RepRapLtd/6DInput/RepRapLtd/Pictures/force-sensor-cad-600x600.jpg

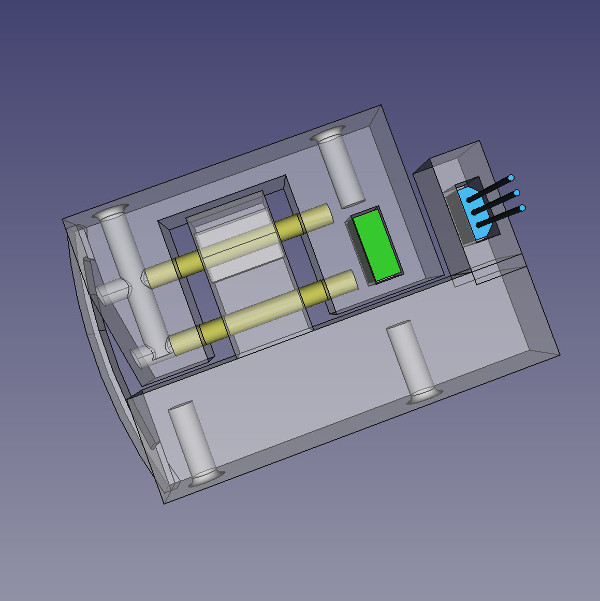
RepRapLtd/Pictures/force-sensor-cad-600x600.jpg
