RepRapLtd/6DInput/RepRapLtd/Pictures/force-sensor-cad.jpg

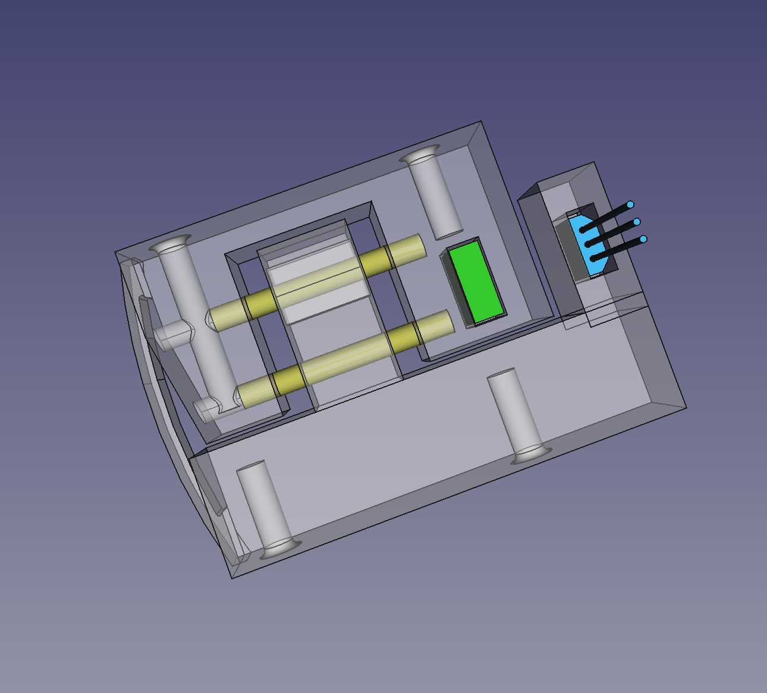
RepRapLtd/Pictures/force-sensor-cad.jpg
