RepRapLtd/6DInput/RepRapLtd/Pictures/force-sensor.jpg

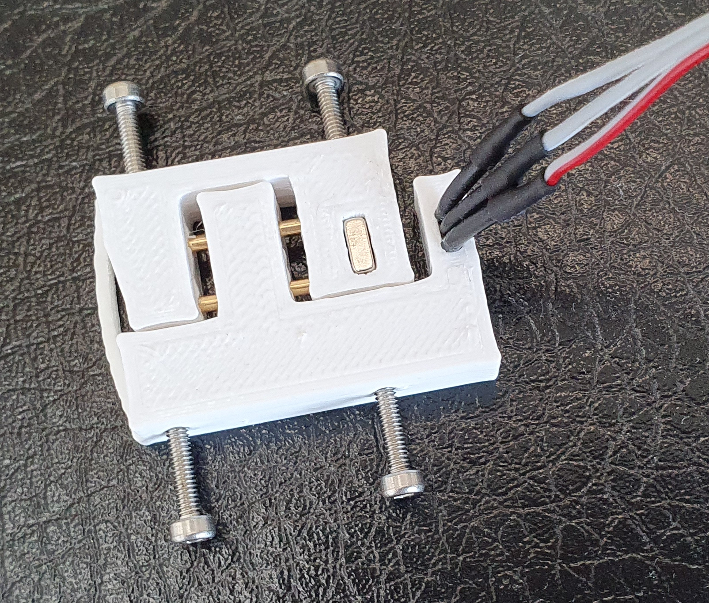
RepRapLtd/Pictures/force-sensor.jpg
