RepRapLtd/6DInput/RepRapLtd/Pictures/nintendo.png

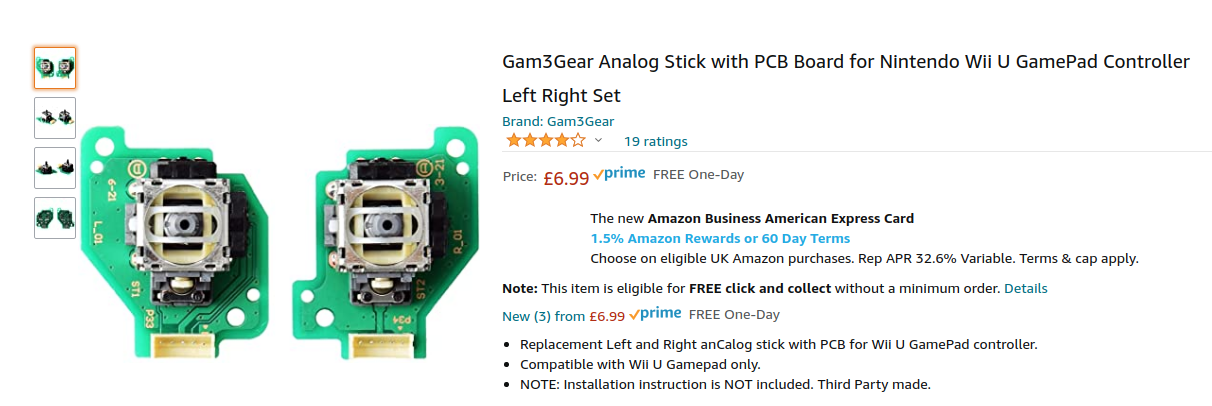
RepRapLtd/Pictures/nintendo.png
