RepRapLtd/6DInput/RepRapLtd/Pictures/v1-cad.jpg

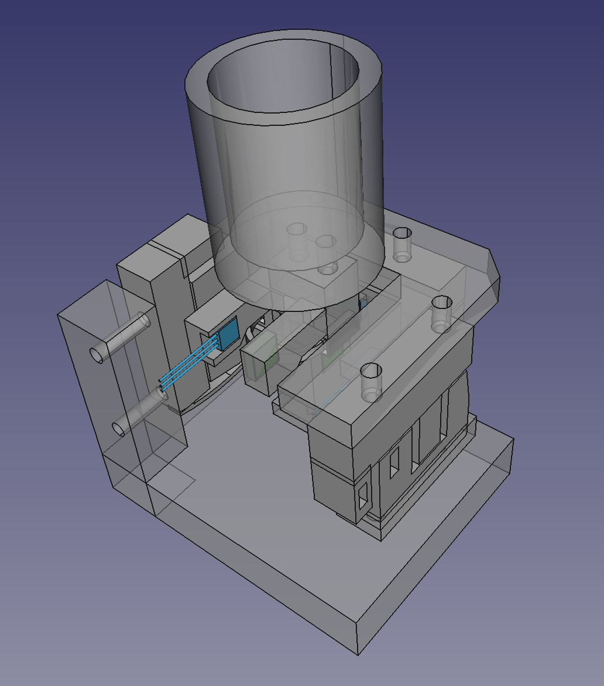
RepRapLtd/Pictures/v1-cad.jpg
