RepRapLtd/6DInput/RepRapLtd/Pictures/v1.jpg

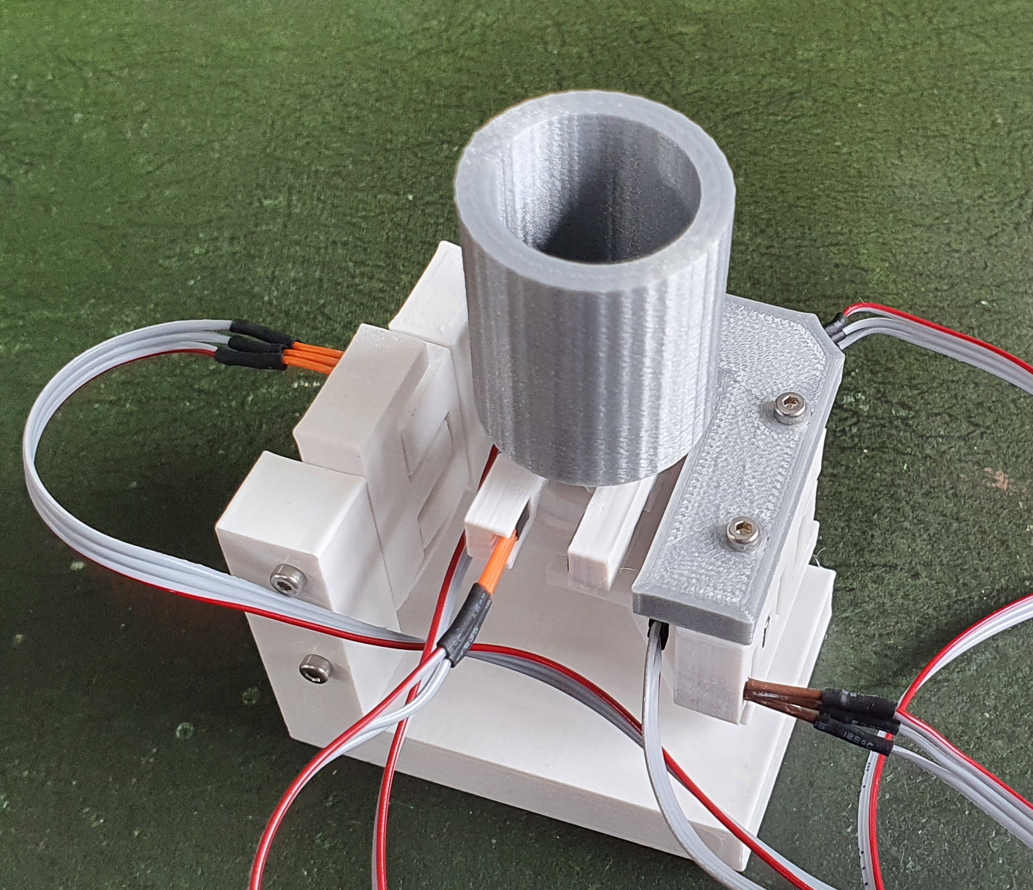
RepRapLtd/Pictures/v1.jpg
