RepRapLtd/6DInput/RepRapLtd/Pictures/XYZ-joystick-CAD-600.png

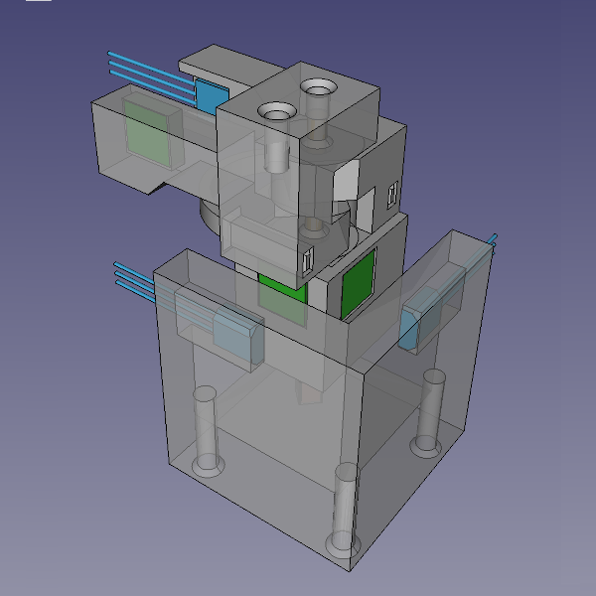
RepRapLtd/Pictures/XYZ-joystick-CAD-600.png
