RepRapLtd/6DInput/RepRapLtd/Mechanics/STLs/6DOF-disc-wright-base.stl

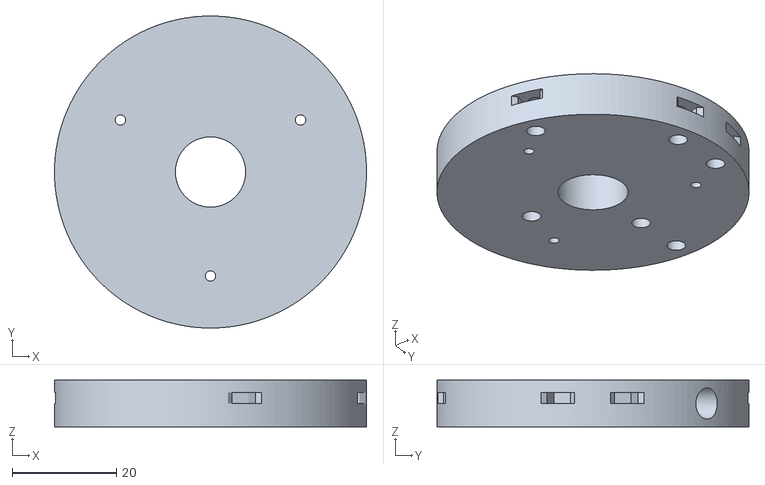
[picture p35: CAD file, 2021-08-13]
RepRapLtd/Mechanics/STLs/6DOF-disc-wright-base.stl
60.0 x 60.0 x 9.00
