RepRapLtd/6DInput/Mechanics/Assembly Experiments/3D Printable Joystick Assembly - Magnetic Encoders/Parts/AS5247UAdapterBoard.FCStd

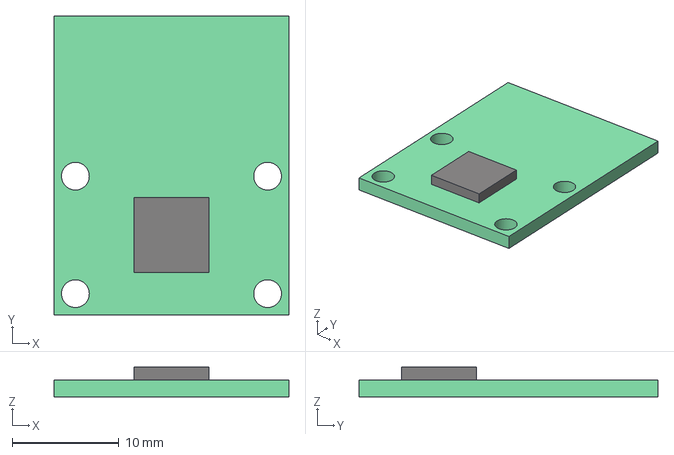
[picture p36: CAD file, 2021-05-03]
Mechanics/Assembly Experiments/3D Printable Joystick Assembly - Magnetic Encoders/Parts/AS5247UAdapterBoard.FCStd
22.0 x 28.0 x 2.80 mm
PCB
IC
