RepRapLtd/6DInput/RepRapLtd/Mechanics/OS3Dmouse-V1.FCStd

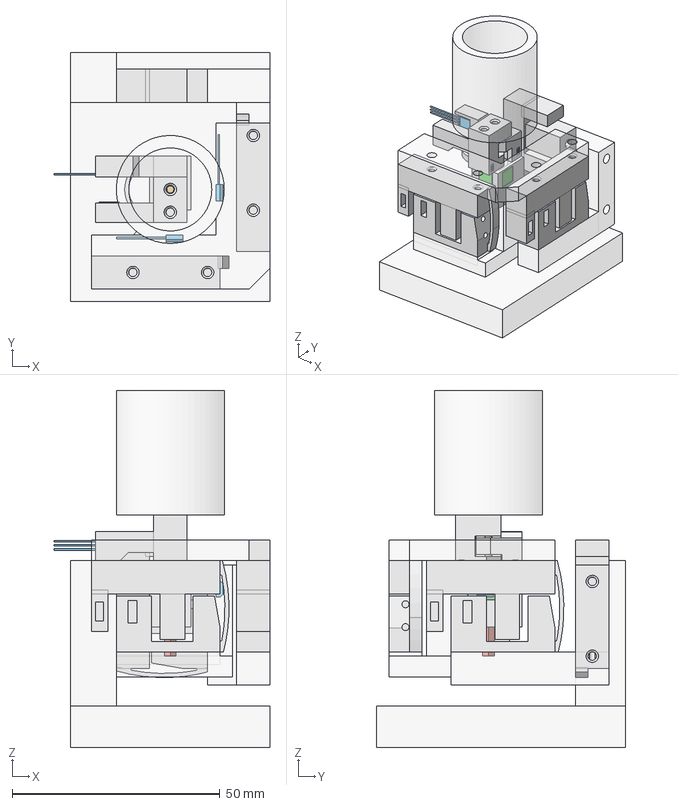
[picture p37: CAD file, 2021-06-14]
RepRapLtd/Mechanics/OS3Dmouse-V1.FCStd
52.0 x 60.0 x 86.0 mm
top-spring
magnet
sensor-OH49E-b
sensor-OH49E-a
magnet-5x5x2-b
magnet-5x5x2-a
bottom-spring
lever
magnet-5x5x2-c
sensor-OH49E-c
rod004
force-sensor
force-sensor001
force-sensor002
handle
XY-link
rot-x-link
YZ-link
base
