RepRapLtd/6DInput/RepRapLtd/Mechanics/STLs/6DoF-disc-base.stl

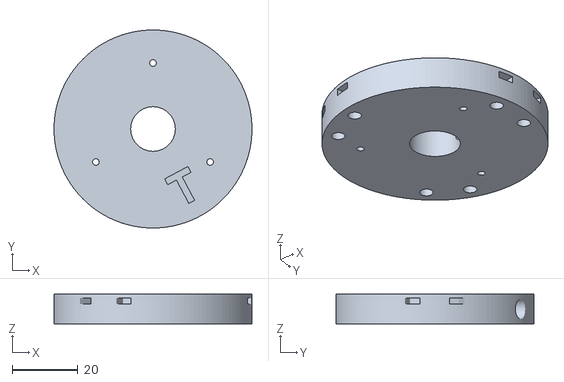
[picture p38: CAD file, 2021-08-02]
RepRapLtd/Mechanics/STLs/6DoF-disc-base.stl
60.0 x 60.0 x 9.00
