RepRapLtd/6DInput/Mechanics/Assembly Experiments/3D Printable Joystick Assembly - Magnetic Encoders/Parts/GimbalMount.FCStd

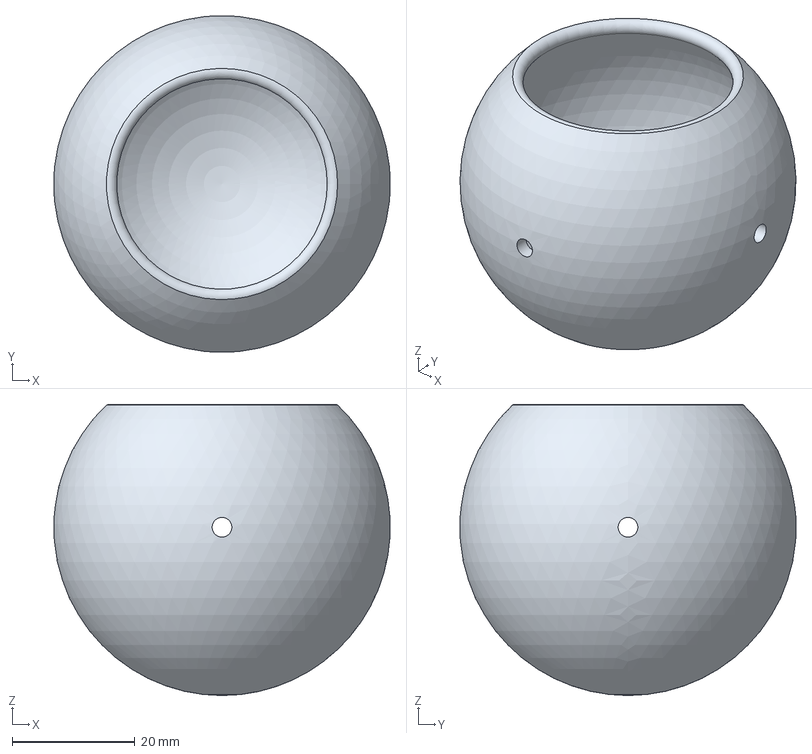
[picture p39: CAD file, 2021-05-03]
Mechanics/Assembly Experiments/3D Printable Joystick Assembly - Magnetic Encoders/Parts/GimbalMount.FCStd
54.7 x 54.7 x 47.4 mm
