RepRapLtd/6DInput/RepRapLtd/Mechanics/6DOF-cones.FCStd

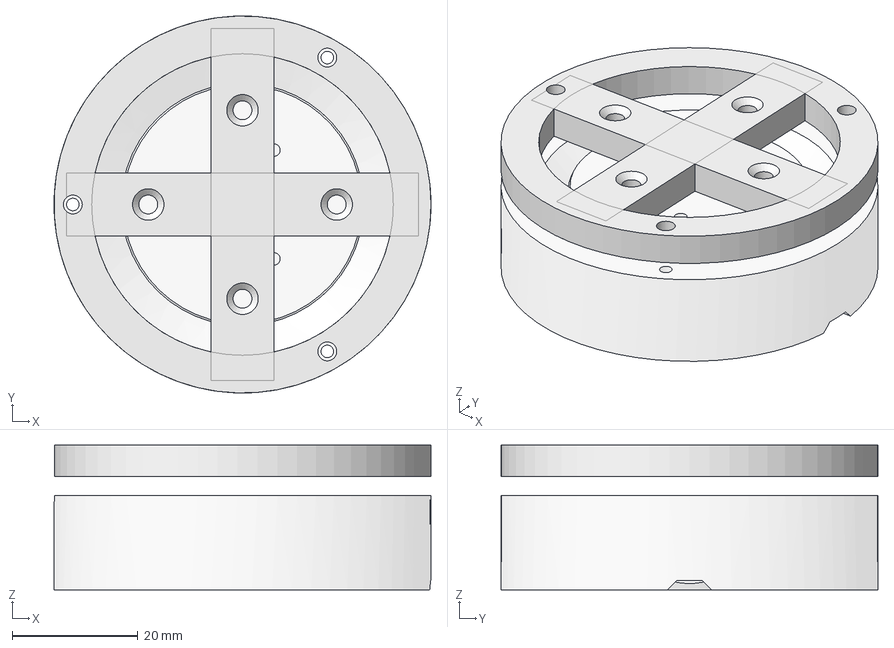
[picture p40: CAD file, 2021-06-11]
RepRapLtd/Mechanics/6DOF-cones.FCStd
60.0 x 60.0 x 23.0 mm
hall-f
magnet-f
calibration
