RepRapLtd/6DInput/RepRapLtd/Mechanics/STLs/6DoF-disc-handle.stl

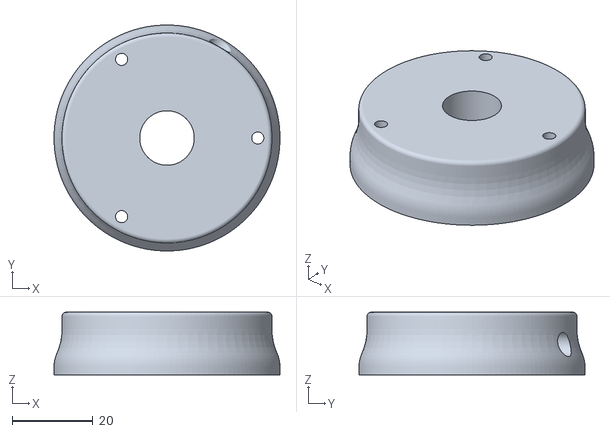
[picture p41: CAD file, 2021-08-02]
RepRapLtd/Mechanics/STLs/6DoF-disc-handle.stl
56.0 x 56.0 x 15.5
