RepRapLtd/6DInput/Mechanics/Assembly Experiments/3D Printable Joystick Assembly - Magnetic Encoders/Parts/DiametricMagnet8x2.5mm.FCStd

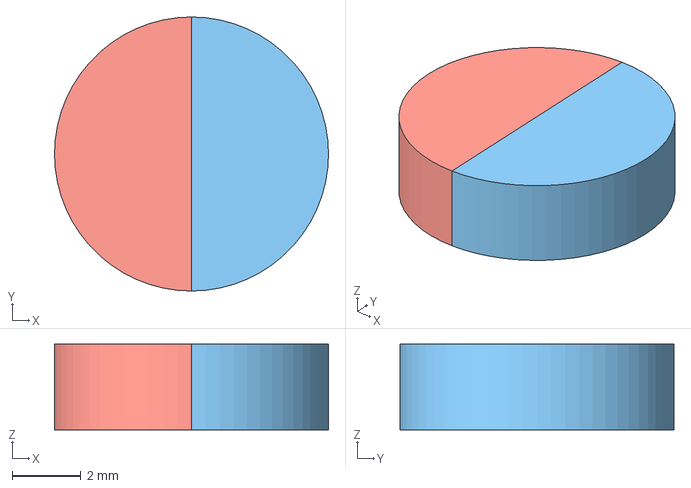
[picture p42: CAD file, 2021-05-03]
Mechanics/Assembly Experiments/3D Printable Joystick Assembly - Magnetic Encoders/Parts/DiametricMagnet8x2.5mm.FCStd
8.00 x 8.00 x 2.50 mm
North
South
