RepRapLtd/6DInput/RepRapLtd/Mechanics/STLs/6DoF-disc-spring-clamp.stl

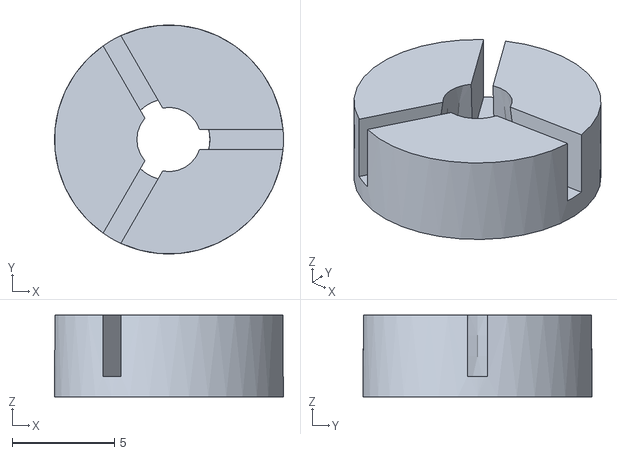
[picture p43: CAD file, 2021-07-16]
RepRapLtd/Mechanics/STLs/6DoF-disc-spring-clamp.stl
11.2 x 11.2 x 4.00
