RepRapLtd/6DInput/RepRapLtd/Mechanics/XYZ-joystick-V1.FCStd

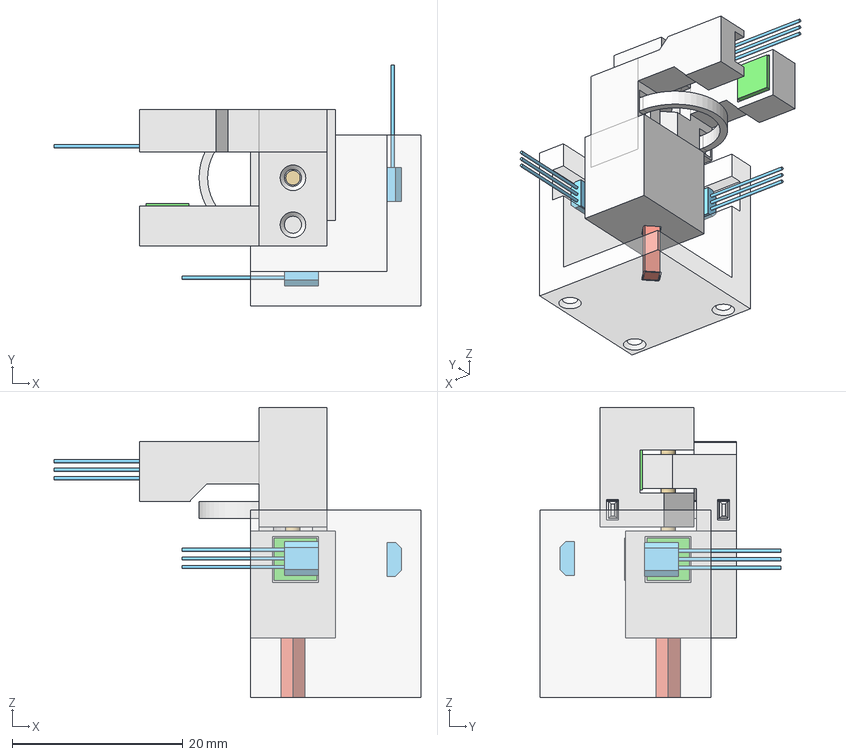
[picture p44: CAD file, 2021-06-11]
RepRapLtd/Mechanics/XYZ-joystick-V1.FCStd
43.0 x 28.2 x 34.0 mm
top-spring
magnet
sensor-OH49E-b
sensor-OH49E-a
magnet-5x5x2-b
magnet-5x5x2-a
bottom-spring
lever
magnet-5x5x2-c
sensor-OH49E-c
rod004
