RepRapLtd/6DInput/Mechanics/Assembly Experiments/3D Printable Joystick Assembly - Magnetic Encoders/Parts/Dial.FCStd

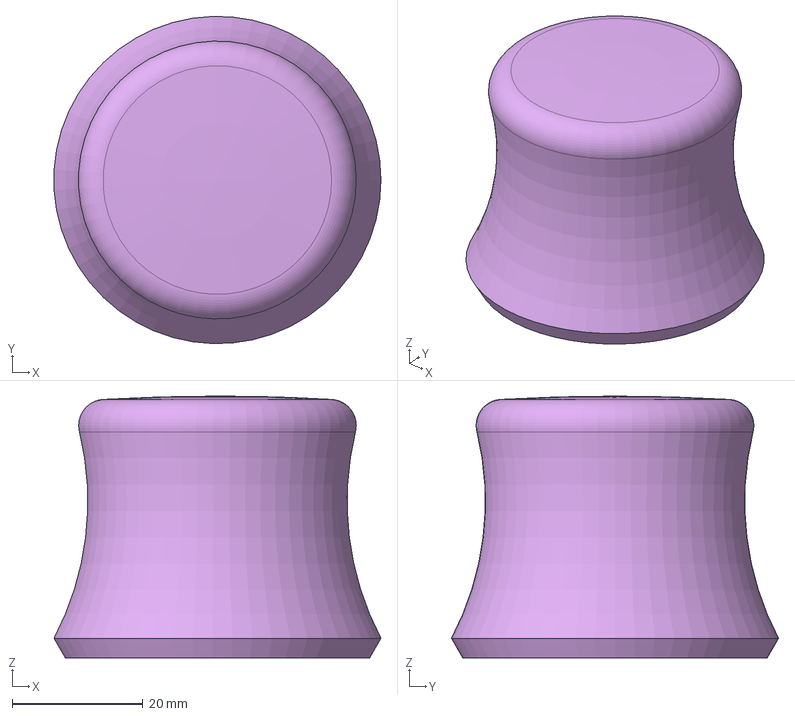
[picture p45: CAD file, 2021-05-03]
Mechanics/Assembly Experiments/3D Printable Joystick Assembly - Magnetic Encoders/Parts/Dial.FCStd
50.0 x 50.0 x 40.0 mm
