RepRapLtd/6DInput/RepRapLtd/Mechanics/STLs/OS3Dmouse-XY-link.stl

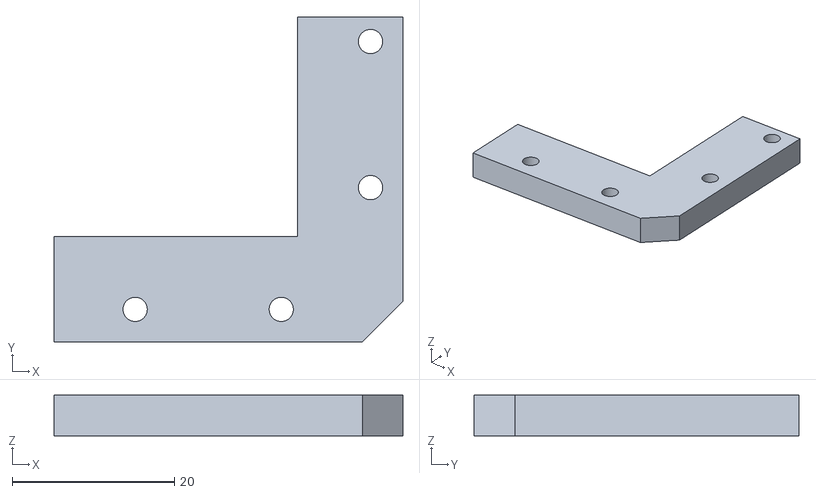
[picture p46: CAD file, 2021-06-14]
RepRapLtd/Mechanics/STLs/OS3Dmouse-XY-link.stl
43.0 x 40.0 x 5.00
