RepRapLtd/6DInput/RepRapLtd/Mechanics/torque-sensor-V3.FCStd

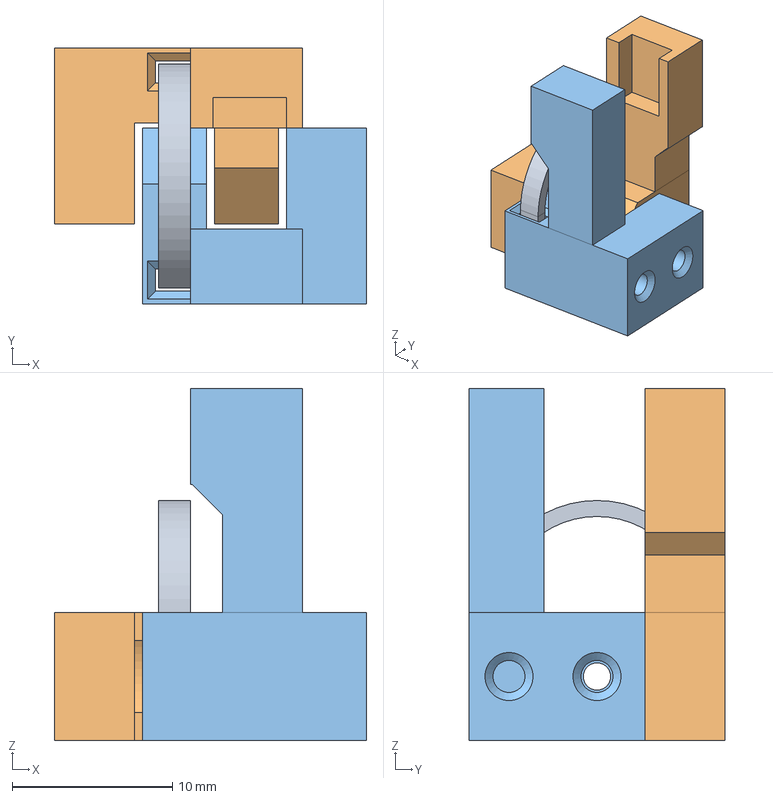
[picture p47: CAD file, 2021-06-10]
RepRapLtd/Mechanics/torque-sensor-V3.FCStd
19.5 x 16.0 x 22.0 mm
spring
hall
magnet
