RepRapLtd/6DInput/RepRapLtd/Mechanics/2D-joystick-V1.FCStd

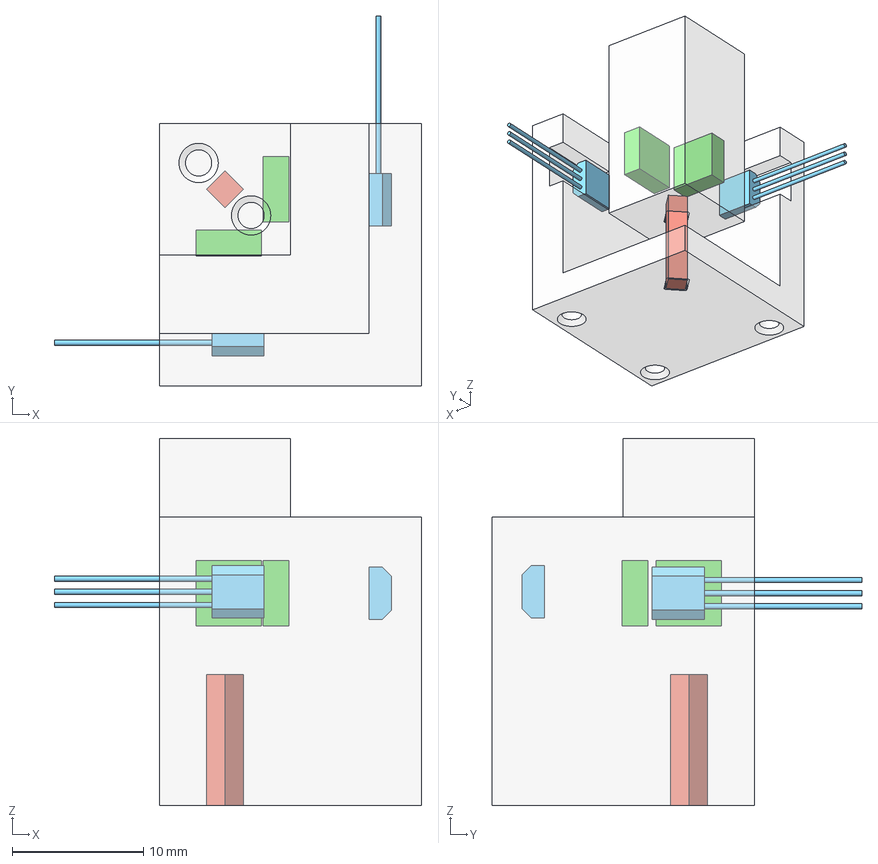
[picture p48: CAD file, 2021-06-08]
RepRapLtd/Mechanics/2D-joystick-V1.FCStd
28.0 x 28.2 x 28.0 mm
spring-0
lever
magnet-5x5x2-a
sensor-OH49E-a
magnet-5x5x2-b
sensor-OH49E-b
