RepRapLtd/6DInput/RepRapLtd/Mechanics/STLs/OS3Dmouse-YZ-link.stl

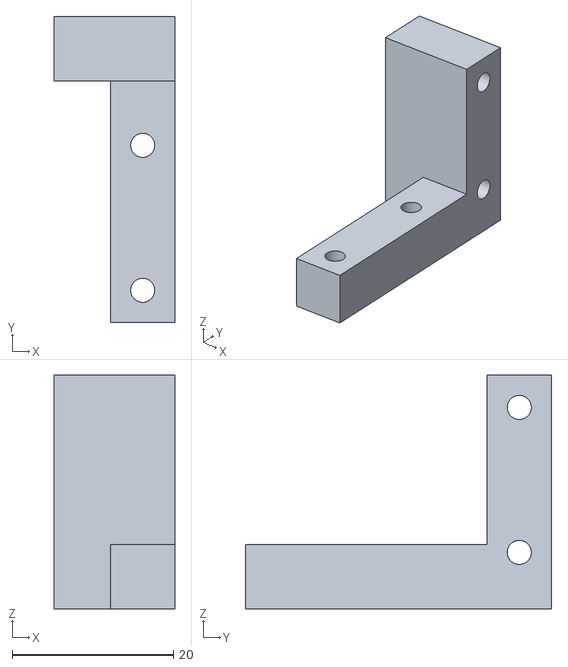
[picture p49: CAD file, 2021-06-14]
RepRapLtd/Mechanics/STLs/OS3Dmouse-YZ-link.stl
15.0 x 38.0 x 29.0
