RepRapLtd/6DInput/RepRapLtd/Mechanics/force-sensor-V1.FCStd

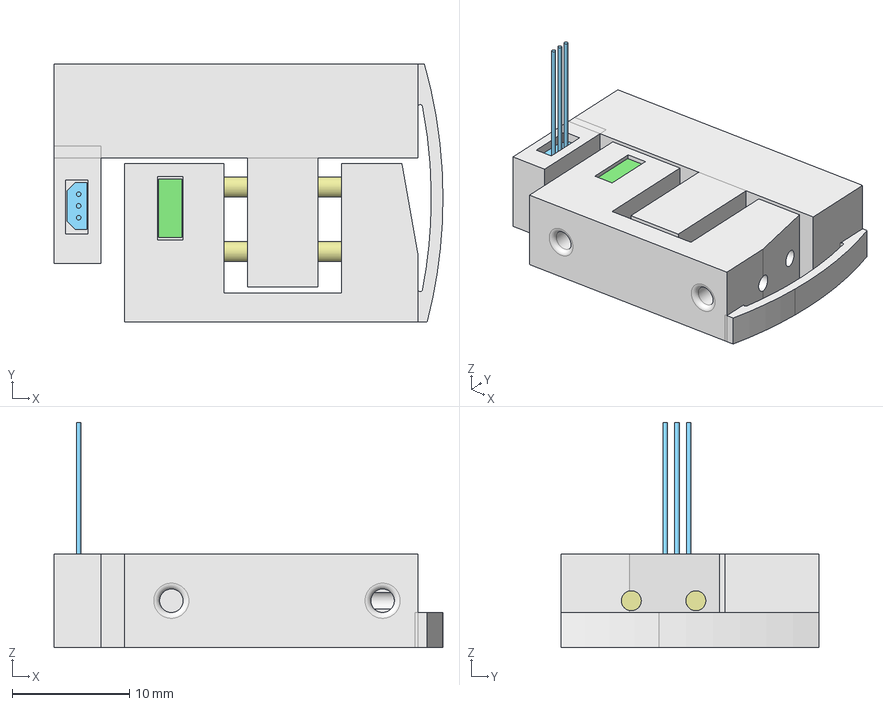
[picture p50: CAD file, 2021-06-05]
RepRapLtd/Mechanics/force-sensor-V1.FCStd
33.1 x 22.0 x 19.2 mm
force-sensor
magnet-5x5x2
sensor-OH49E
brass-rod-1
brass-rod-2
