RepRapLtd/6DInput/RepRapLtd/Mechanics/STLs/OS3Dmouse-rotX-link.stl

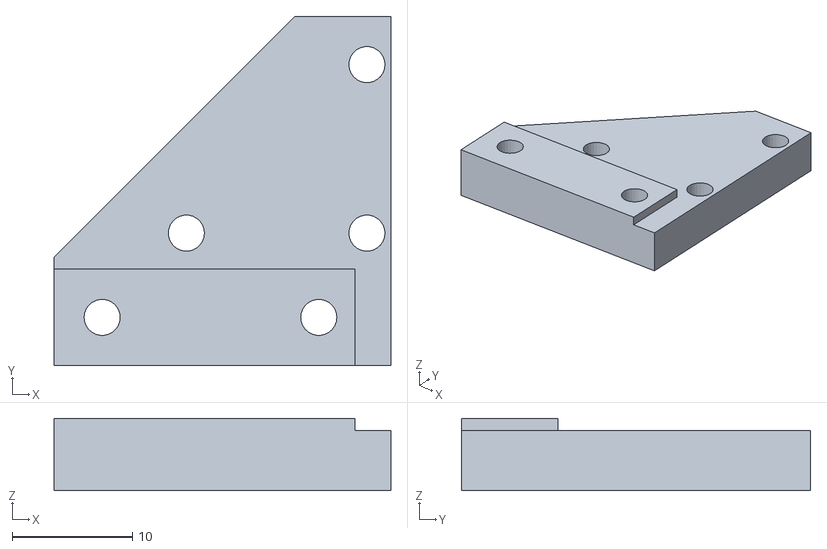
[picture p51: CAD file, 2021-06-14]
RepRapLtd/Mechanics/STLs/OS3Dmouse-rotX-link.stl
28.0 x 29.0 x 6.00
