RepRapLtd/6DInput/RepRapLtd/Mechanics/STLs/OS3Dmouse-base.stl

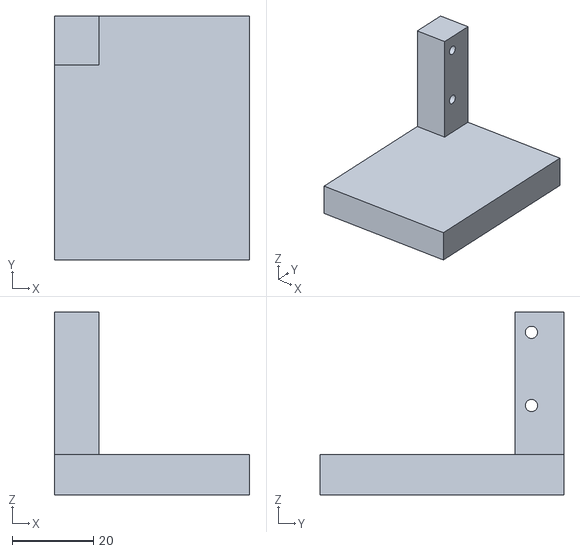
[picture p52: CAD file, 2021-06-14]
RepRapLtd/Mechanics/STLs/OS3Dmouse-base.stl
48.0 x 60.0 x 45.0
