RepRapLtd/6DInput/RepRapLtd/Mechanics/calibration-jig.FCStd

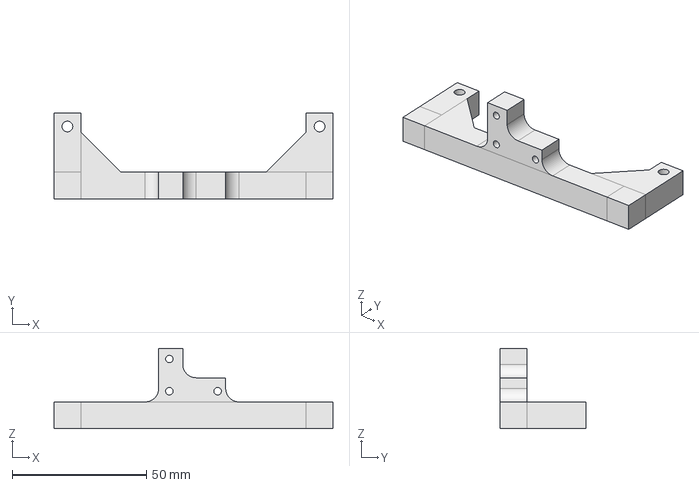
[picture p53: CAD file, 2021-05-28]
RepRapLtd/Mechanics/calibration-jig.FCStd
104.0 x 32.0 x 30.0 mm
