RepRapLtd/6DInput/RepRapLtd/Mechanics/STLs/OS3Dmouse-handle.stl

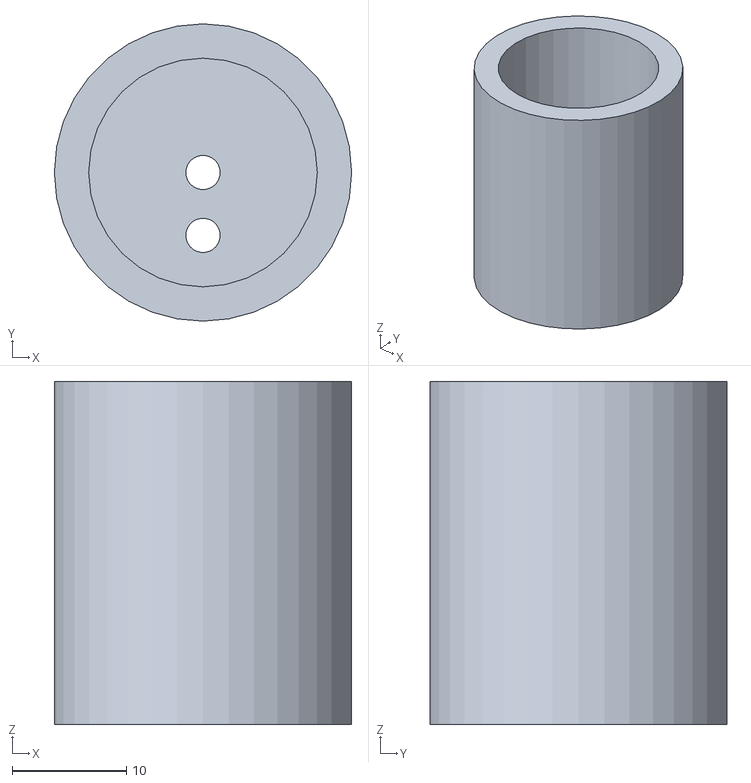
[picture p54: CAD file, 2021-06-14]
RepRapLtd/Mechanics/STLs/OS3Dmouse-handle.stl
26.0 x 26.0 x 30.0
