RepRapLtd/6DInput/RepRapLtd/Mechanics/octahedron-design.FCStd

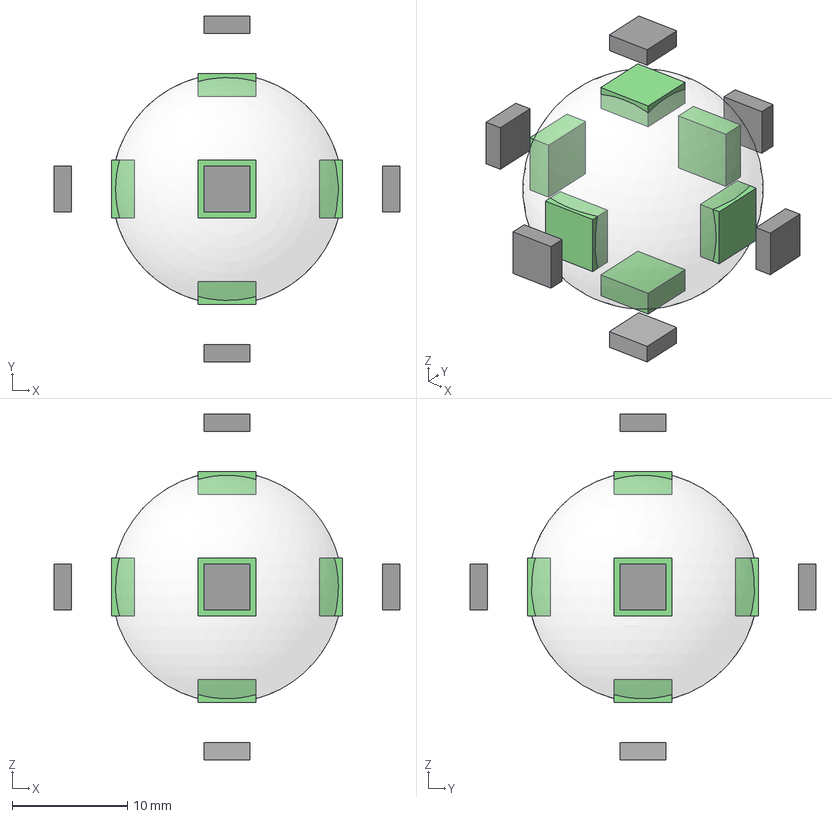
[picture p55: CAD file, 2021-05-21]
RepRapLtd/Mechanics/octahedron-design.FCStd
30.0 x 30.0 x 30.0 mm
