RepRapLtd/6DInput/RepRapLtd/Mechanics/STLs/6D-cones-magnet.stl

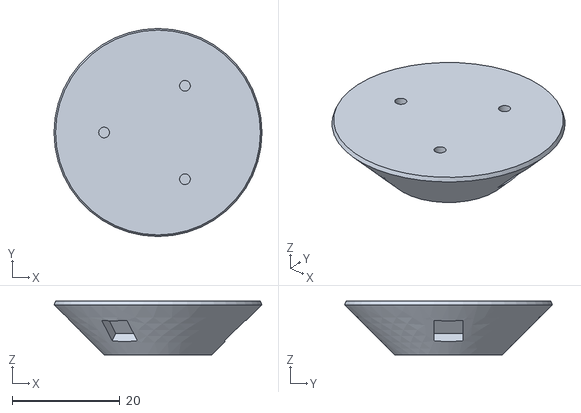
[picture p56: CAD file, 2021-06-11]
RepRapLtd/Mechanics/STLs/6D-cones-magnet.stl
38.6 x 38.6 x 10.0
