RepRapLtd/6DInput/RepRapLtd/Mechanics/force-displacement-sensor-V2.FCStd

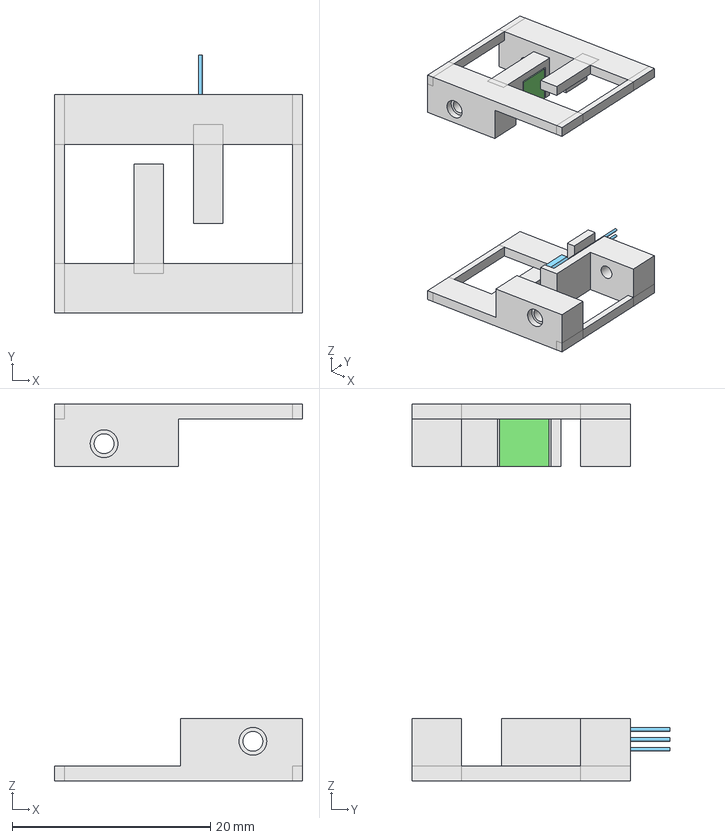
[picture p57: CAD file, 2021-05-21]
RepRapLtd/Mechanics/force-displacement-sensor-V2.FCStd
25.0 x 26.0 x 38.0 mm
hall
magnet
mag
sensor
