RepRapLtd/6DInput/RepRapLtd/Mechanics/STLs/6D-cones-calibration.stl

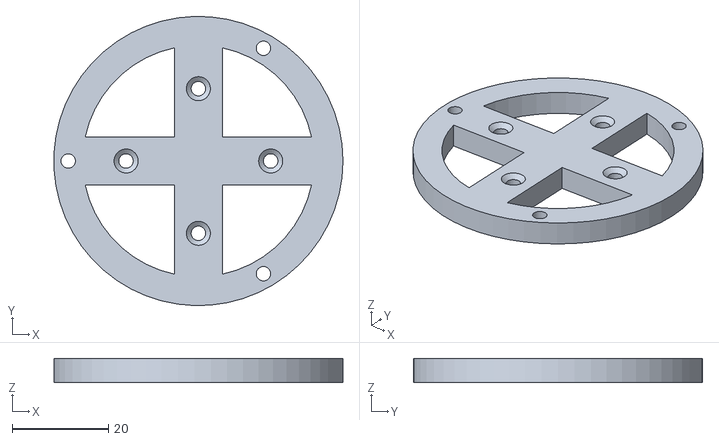
[picture p58: CAD file, 2021-06-11]
RepRapLtd/Mechanics/STLs/6D-cones-calibration.stl
60.0 x 60.0 x 5.00
