RepRapLtd/6DInput/RepRapLtd/Mechanics/STLs/6D-cones-hall.stl

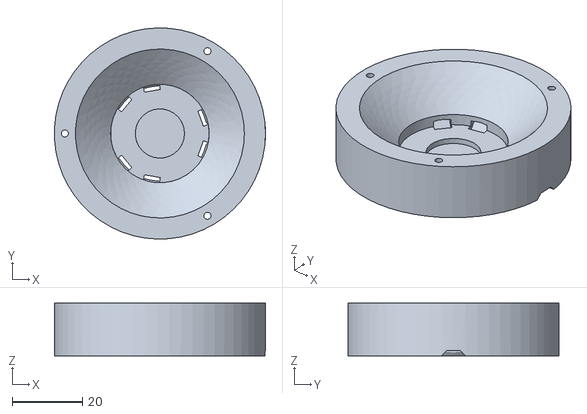
[picture p59: CAD file, 2021-06-11]
RepRapLtd/Mechanics/STLs/6D-cones-hall.stl
60.0 x 60.0 x 15.0
