RepRapLtd/6DInput/RepRapLtd/Mechanics/Hall-ring-experiment-holder.FCStd

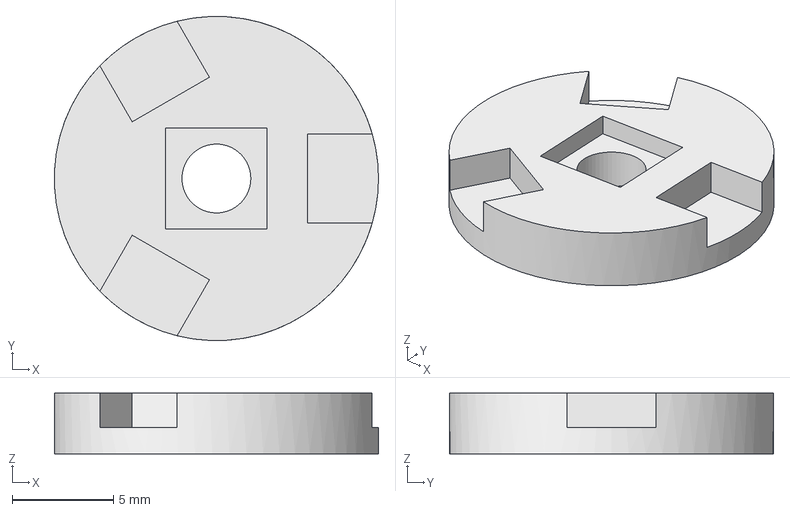
[picture p60: CAD file, 2021-05-11]
RepRapLtd/Mechanics/Hall-ring-experiment-holder.FCStd
16.0 x 16.0 x 3.00 mm
