RepRapLtd/6DInput/RepRapLtd/Mechanics/STLs/torque-hall.stl

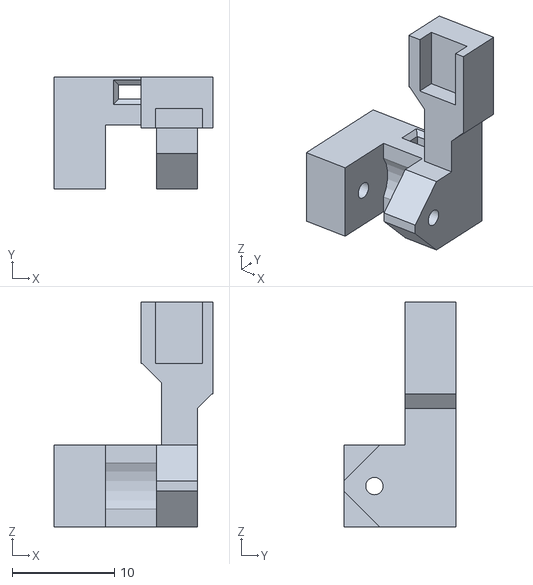
[picture p61: CAD file, 2021-06-10]
RepRapLtd/Mechanics/STLs/torque-hall.stl
15.5 x 11.0 x 22.0
