RepRapLtd/6DInput/RepRapLtd/Mechanics/STLs/XYZ-joystick-twist-spring.stl

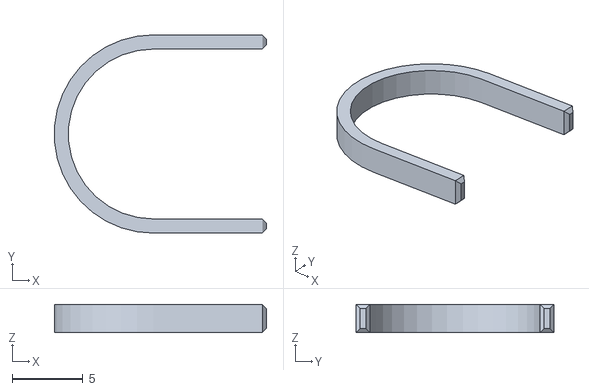
[picture p62: CAD file, 2021-06-10]
RepRapLtd/Mechanics/STLs/XYZ-joystick-twist-spring.stl
15.0 x 14.0 x 2.00
