RepRapLtd/6DInput/RepRapLtd/Mechanics/STLs/torque-magnet.stl

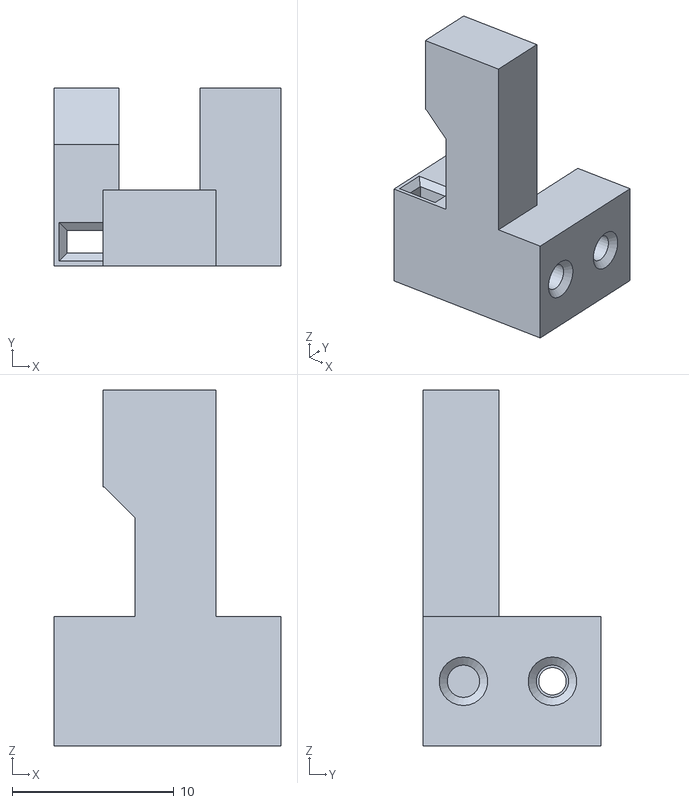
[picture p63: CAD file, 2021-06-10]
RepRapLtd/Mechanics/STLs/torque-magnet.stl
14.0 x 11.0 x 22.0
