RepRapLtd/6DInput/RepRapLtd/Mechanics/STLs/XYZ-joystick-lever.stl

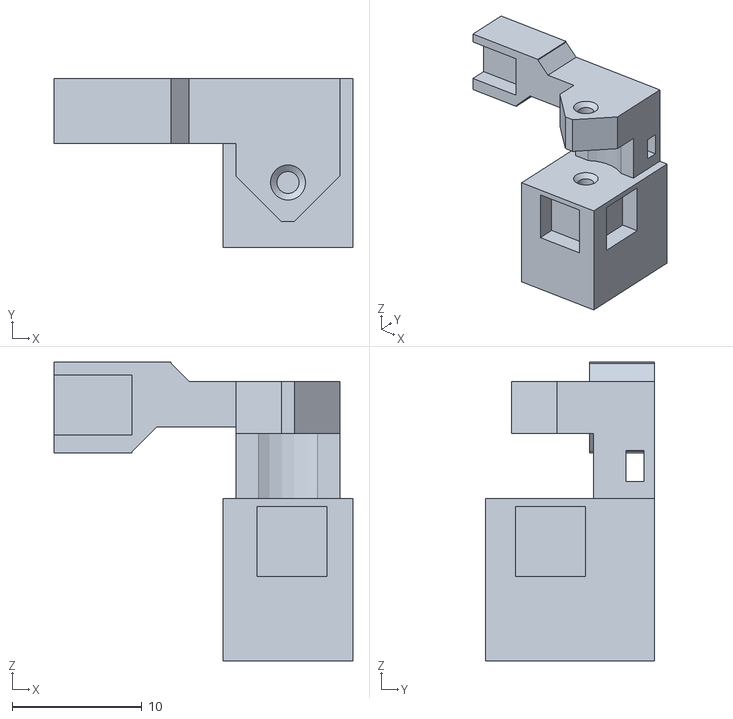
[picture p64: CAD file, 2021-06-10]
RepRapLtd/Mechanics/STLs/XYZ-joystick-lever.stl
23.0 x 13.0 x 23.0
