RepRapLtd/6DInput/RepRapLtd/Mechanics/STLs/joystick-lever.stl

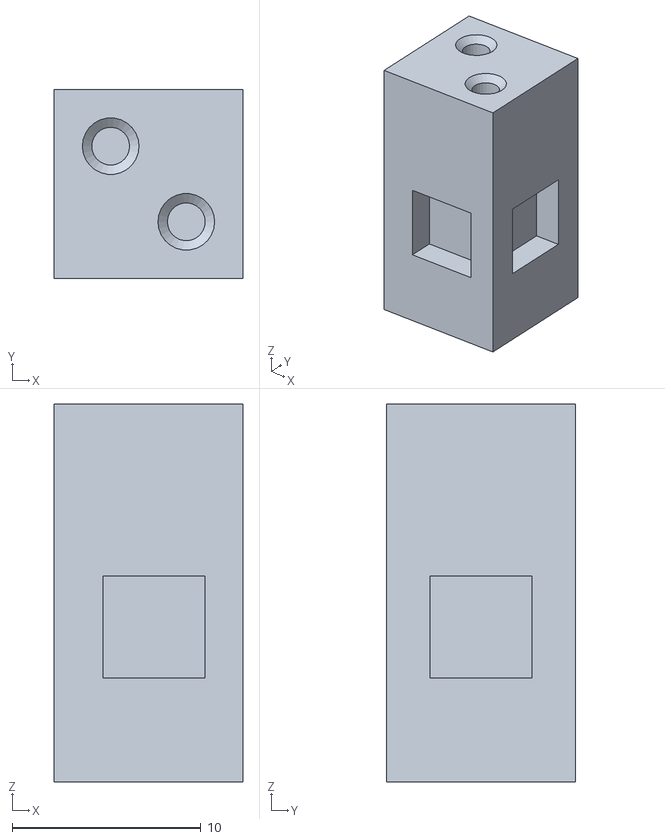
[picture p65: CAD file, 2021-06-08]
RepRapLtd/Mechanics/STLs/joystick-lever.stl
10.0 x 10.0 x 20.0
