RepRapLtd/6DInput/RepRapLtd/Mechanics/STLs/joystick-body.stl

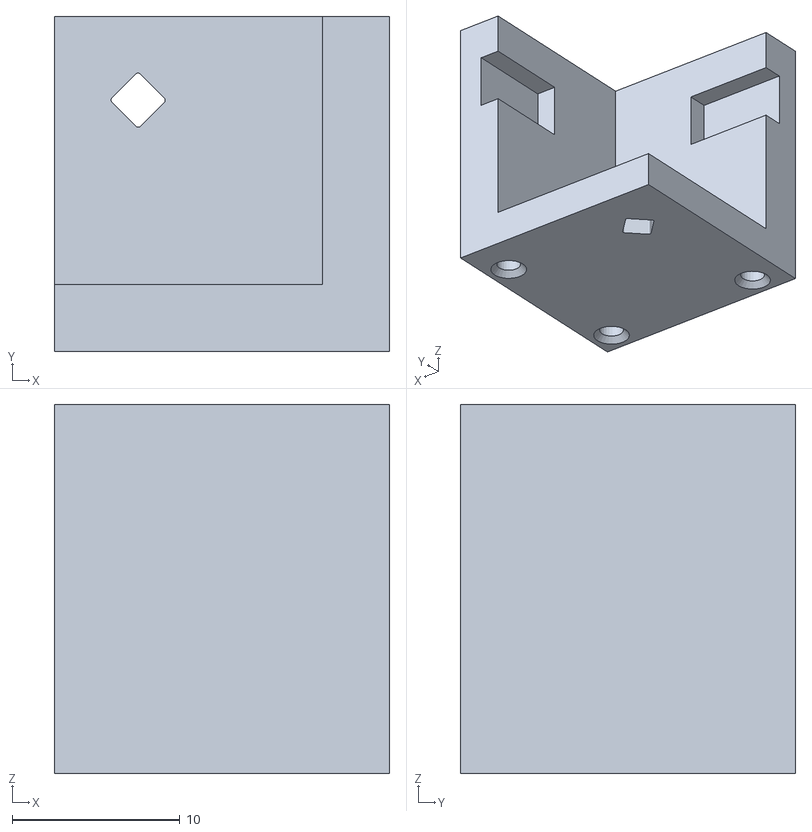
[picture p66: CAD file, 2021-06-08]
RepRapLtd/Mechanics/STLs/joystick-body.stl
20.0 x 20.0 x 22.0
