RepRapLtd/6DInput/RepRapLtd/Mechanics/STLs/joystick-spring.stl

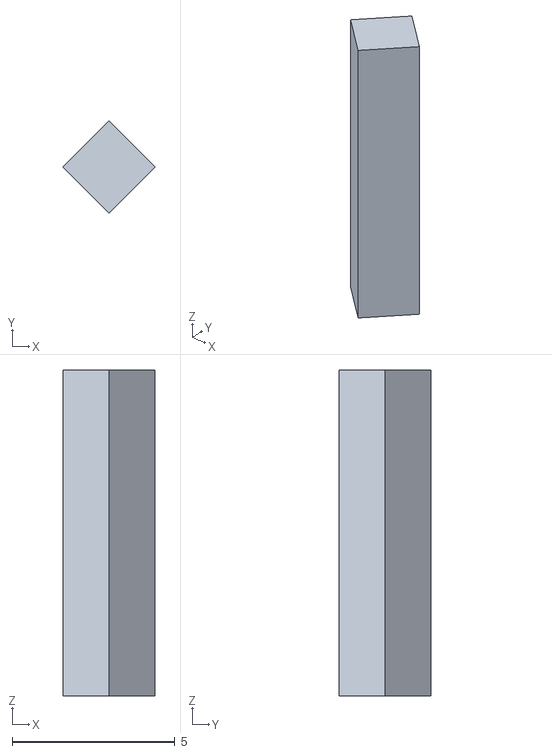
[picture p67: CAD file, 2021-06-08]
RepRapLtd/Mechanics/STLs/joystick-spring.stl
2.83 x 2.83 x 10.0
