RepRapLtd/6DInput/RepRapLtd/Mechanics/STLs/force-sensor.stl

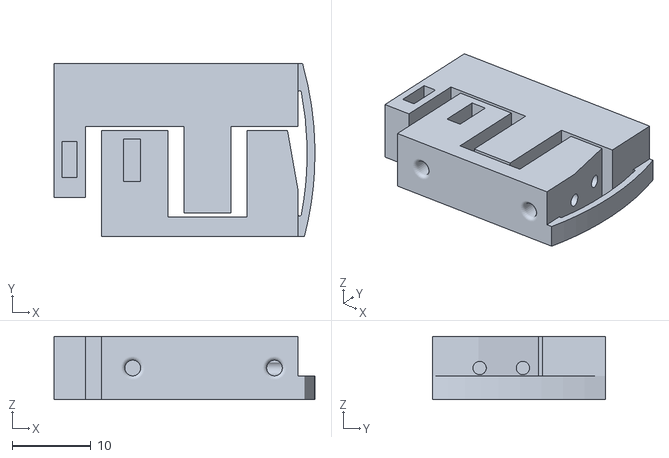
[picture p68: CAD file, 2021-05-28]
RepRapLtd/Mechanics/STLs/force-sensor.stl
33.1 x 22.0 x 8.00
