RepRapLtd/6DInput/Experiments/Geometry Tester/Example results/Magnet Distances.png

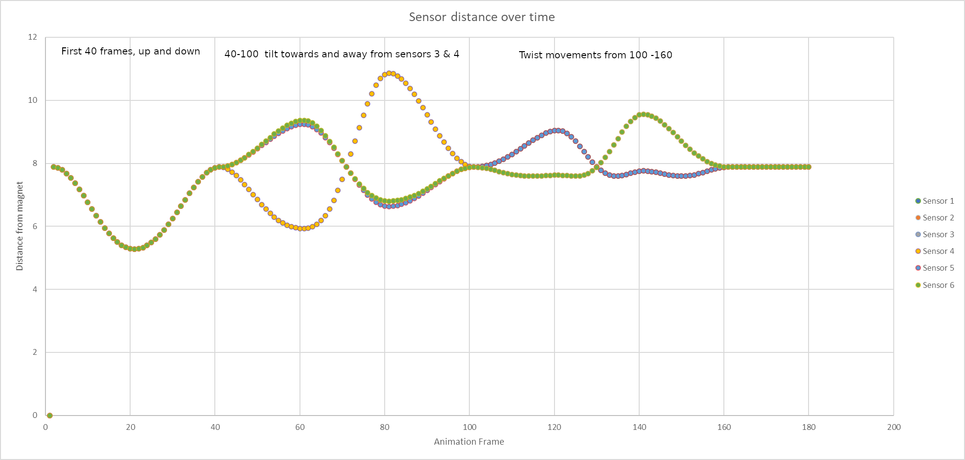
Experiments/Geometry Tester/Example results/Magnet Distances.png
