RepRapLtd/6DInput/RepRapLtd/Experiments/TorqueSensor/hinge-insert.jpg

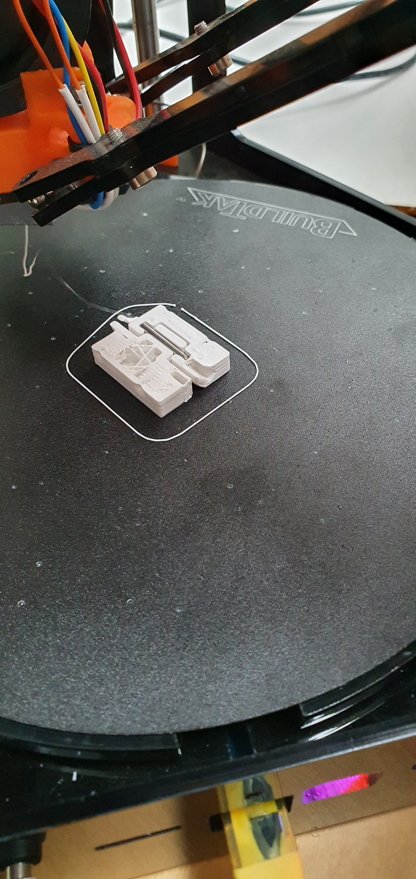
RepRapLtd/Experiments/TorqueSensor/hinge-insert.jpg
